f321x/offline-LightningATM-esp32/assets/Photos/ATM_Photo_2.jpg

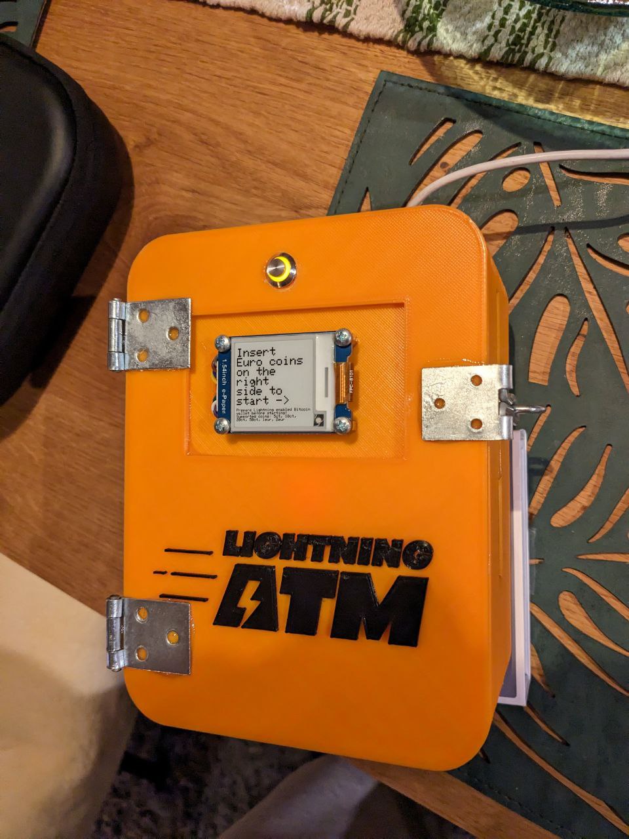
assets/Photos/ATM_Photo_2.jpg
