f321x/offline-LightningATM-esp32/include/fossa_crypto.hpp

#pragma once

#include <mbedtls/aes.h>
#include <mbedtls/md5.h>
#include <Arduino.h>
#include <cstring>
#include "Bitcoin.h"
#include "util.hpp"


String makeLNURLLegacy(String secretATM, float total, String baseURLATM);
String makeLNURLFossa(String secretATM, float total, String baseURLATM);
