f321x/offline-LightningATM-esp32/src/util.cpp

#include "util.hpp"

void to_upper(char* arr)
{
    for (size_t i = 0; i < strlen(arr); i++)
    {
        if (arr[i] >= 'a' && arr[i] <= 'z')
        {
            arr[i] = arr[i] - 'a' + 'A';
        }
    }
}
